majarspeed/Voron-EVA-conversion/STL/LGX/VCv1_top_lgx_mount.stl

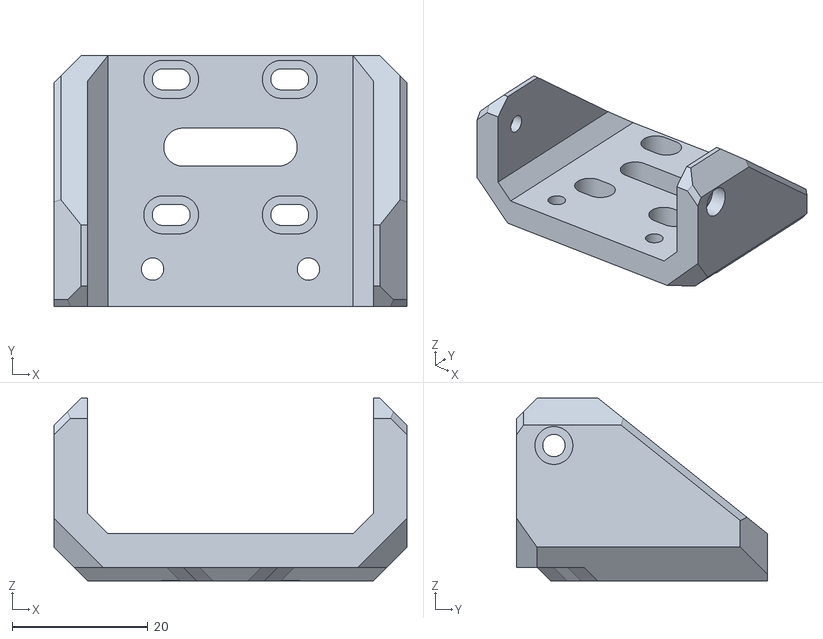
[picture p18: CAD file, 2022-01-29]
STL/LGX/VCv1_top_lgx_mount.stl
52.1 x 37.0 x 27.0
