majarspeed/Voron-EVA-conversion/STL/U face Voron part.stl

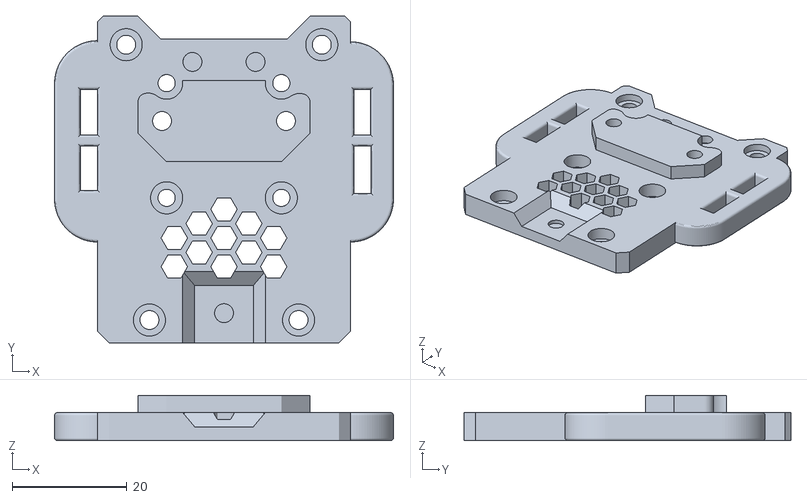
[picture p19: CAD file, 2022-02-09]
STL/U face Voron part.stl
59.1 x 57.0 x 7.90
