majarspeed/Voron-EVA-conversion/UserMod/DoubleT/Orbiter 2.0 backplate.stl

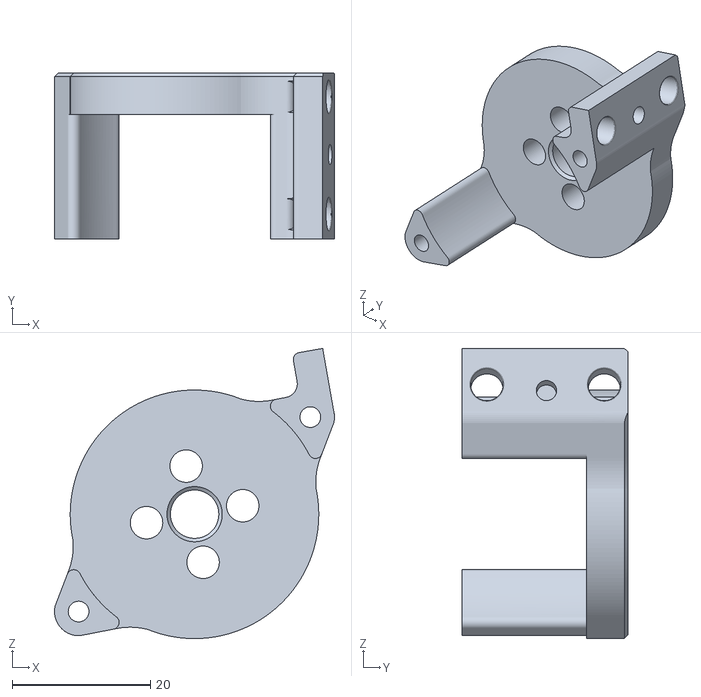
[picture p20: CAD file, 2022-03-22]
UserMod/DoubleT/Orbiter 2.0 backplate.stl
40.6 x 24.0 x 42.0
