majarspeed/Voron-EVA-conversion/STL/Klicky/Dock Sidemount fixed v2.stl

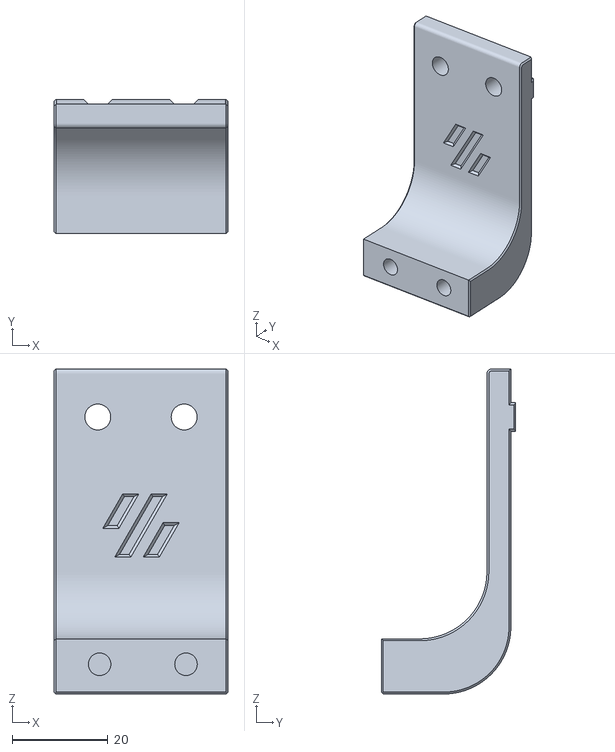
[picture p21: CAD file, 2022-01-29]
STL/Klicky/Dock Sidemount fixed v2.stl
36.3 x 28.0 x 67.7
