majarspeed/Voron-EVA-conversion/STL/Universal Spacer.stl

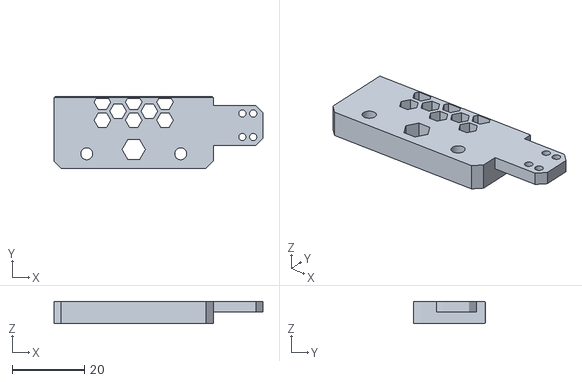
[picture p22: CAD file, 2022-02-07]
STL/Universal Spacer.stl
57.8 x 19.8 x 6.20
