majarspeed/Voron-EVA-conversion/UserMod/DoubleT/cable_holder_v1 v1.stl

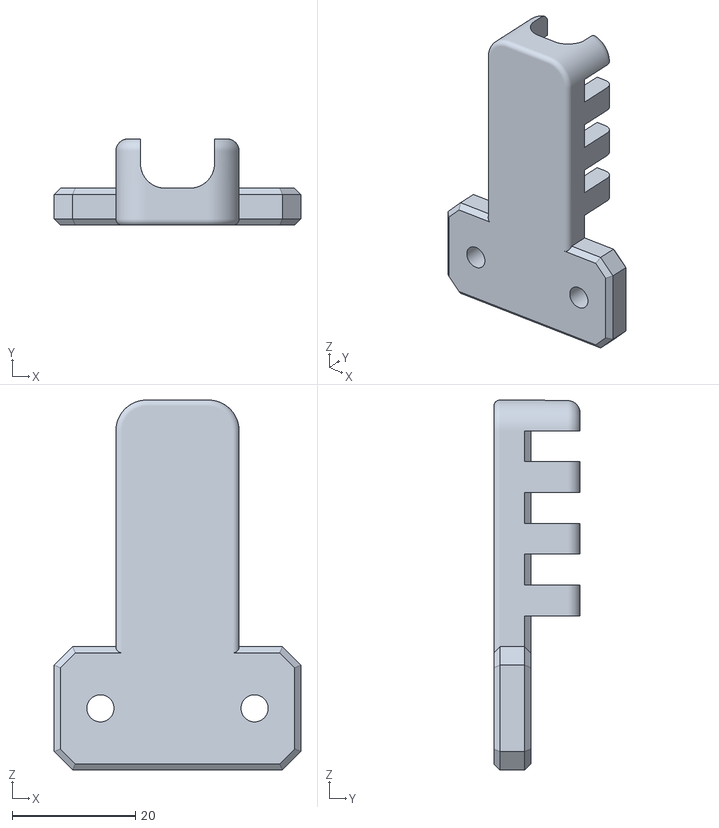
[picture p23: CAD file, 2022-03-22]
UserMod/DoubleT/cable_holder_v1 v1.stl
40.0 x 14.0 x 60.0
