majarspeed/Voron-EVA-conversion/STL/Klicky/Klick side mount adapter.stl

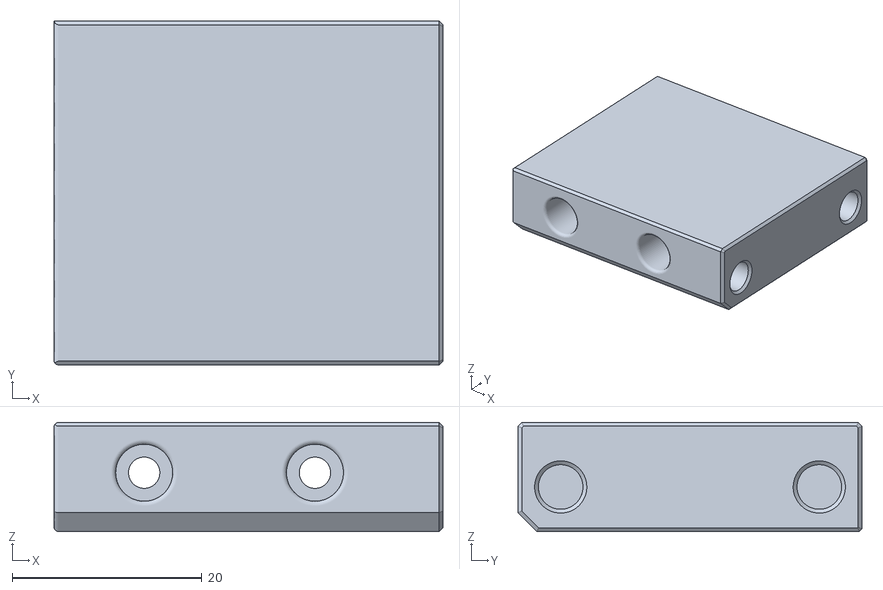
[picture p24: CAD file, 2022-01-29]
STL/Klicky/Klick side mount adapter.stl
41.0 x 36.3 x 11.5
