majarspeed/Voron-EVA-conversion/STL/shroud.stl

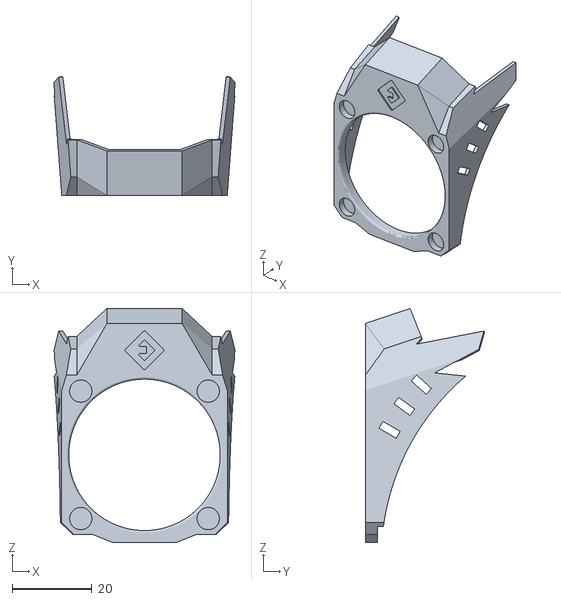
[picture p25: CAD file, 2022-02-07]
STL/shroud.stl
45.4 x 29.9 x 58.7
