majarspeed/Voron-EVA-conversion/UserMod/DoubleT/Belt Clamp.stl

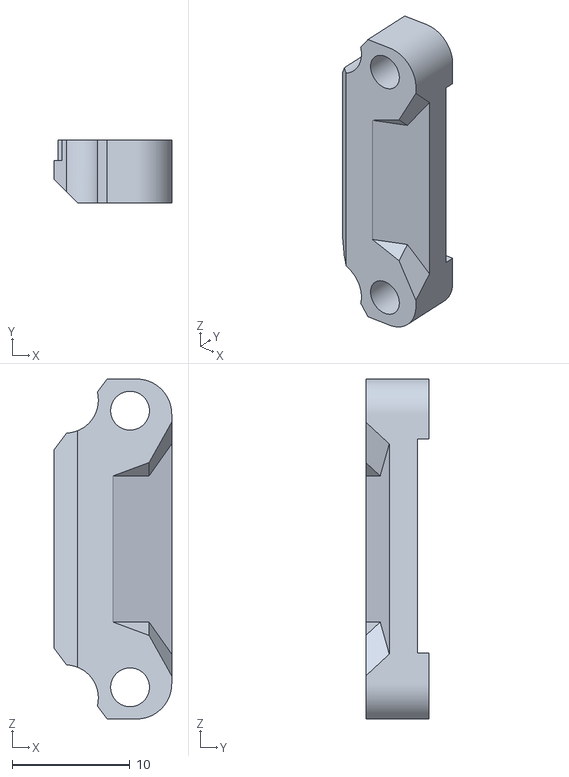
[picture p26: CAD file, 2022-02-04]
UserMod/DoubleT/Belt Clamp.stl
10.0 x 5.40 x 28.9
