majarspeed/Voron-EVA-conversion/STL/VCv1_unversal_cable_mount.stl

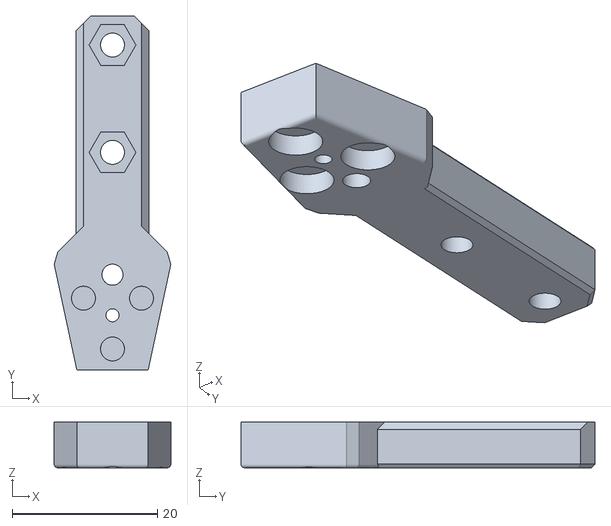
[picture p27: CAD file, 2022-01-29]
STL/VCv1_unversal_cable_mount.stl
16.1 x 48.8 x 6.30
