majarspeed/Voron-EVA-conversion/UserMod/DoubleT/Voron_U-face_mpart_he-block.stl

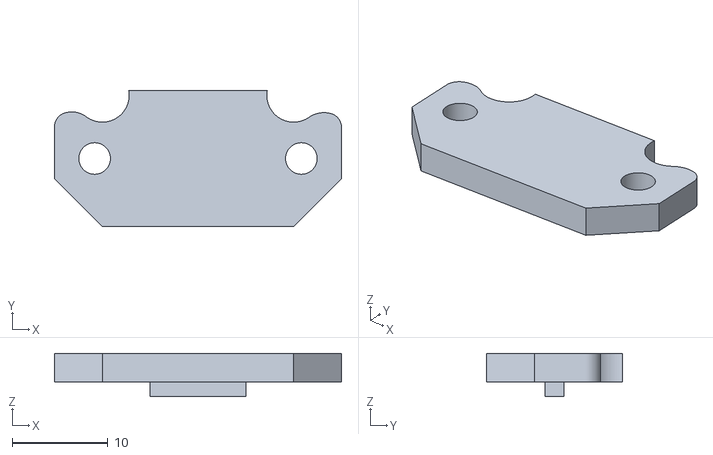
[picture p28: CAD file, 2022-02-04]
UserMod/DoubleT/Voron_U-face_mpart_he-block.stl
30.0 x 14.2 x 4.50
