majarspeed/Voron-EVA-conversion/STL/VCv1_Corexy_short_back.stl

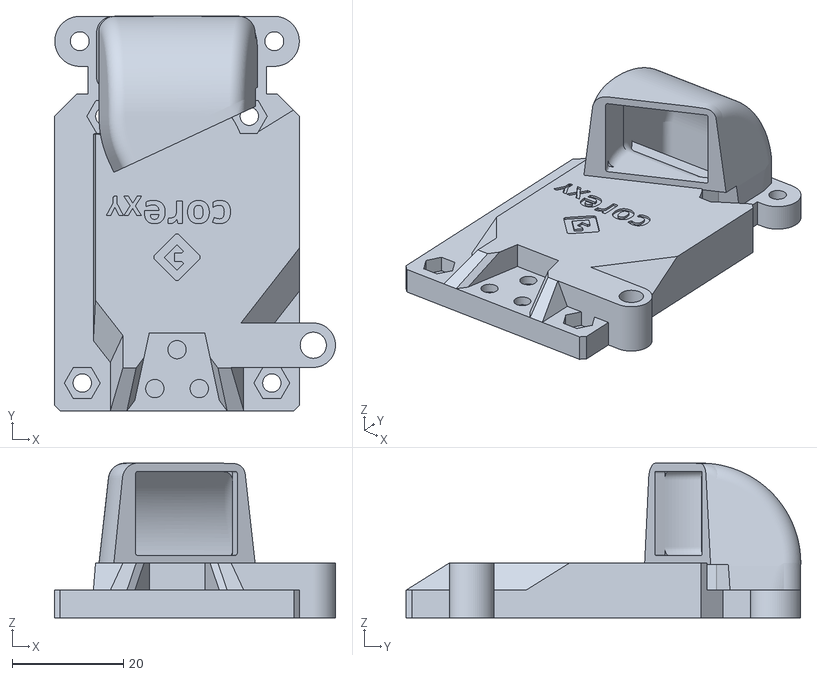
[picture p29: CAD file, 2022-01-29]
STL/VCv1_Corexy_short_back.stl
50.6 x 71.0 x 27.9
