majarspeed/Voron-EVA-conversion/STL/VCv1_bottom_mgn12_short_duct.stl

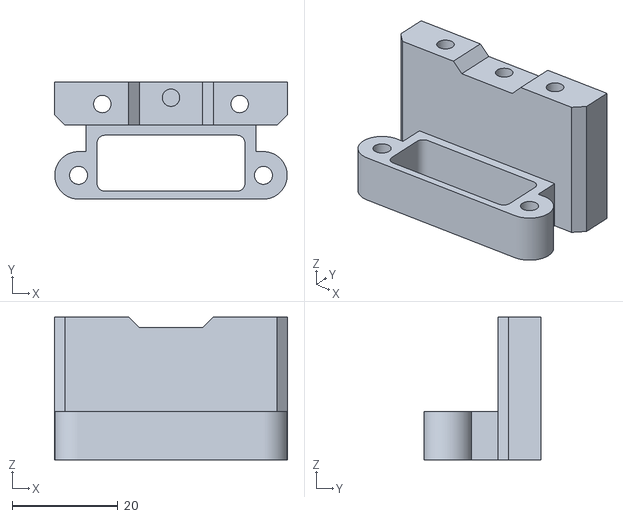
[picture p30: CAD file, 2022-01-29]
STL/VCv1_bottom_mgn12_short_duct.stl
44.1 x 22.2 x 27.0
