majarspeed/Voron-EVA-conversion/STL/VCv1_cable_holder.stl

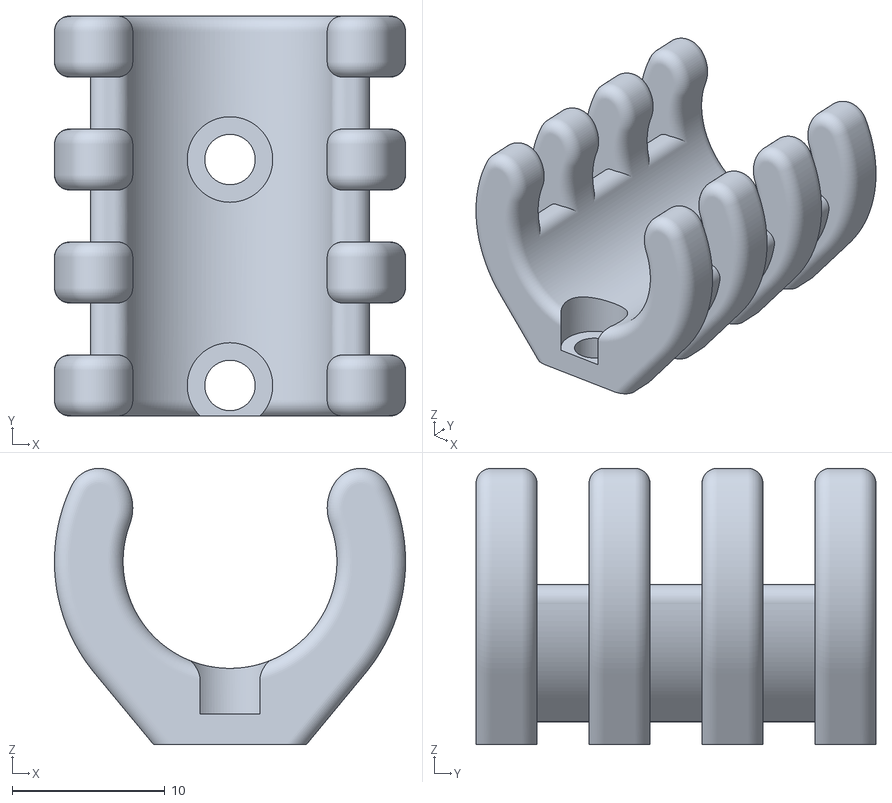
[picture p31: CAD file, 2022-01-29]
STL/VCv1_cable_holder.stl
23.0 x 26.2 x 18.1
